miroslawwaldowski/WeatherStation/Weather_Station_Visualisation/Weather_Station_Electronics.png

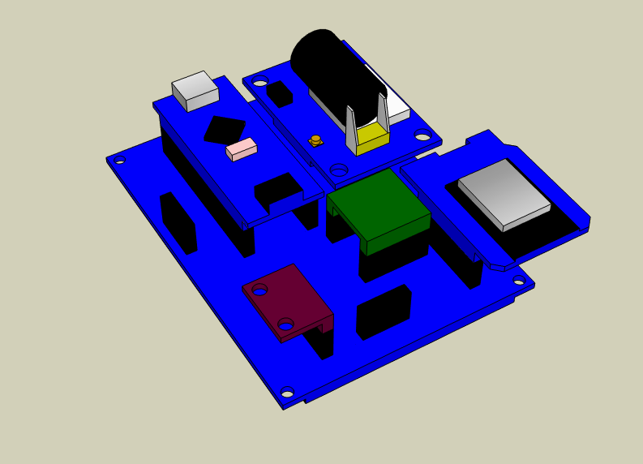
Weather_Station_Visualisation/Weather_Station_Electronics.png
