miroslawwaldowski/WeatherStation/Weather_Station_Visualisation/Weather_Station_Interior.png

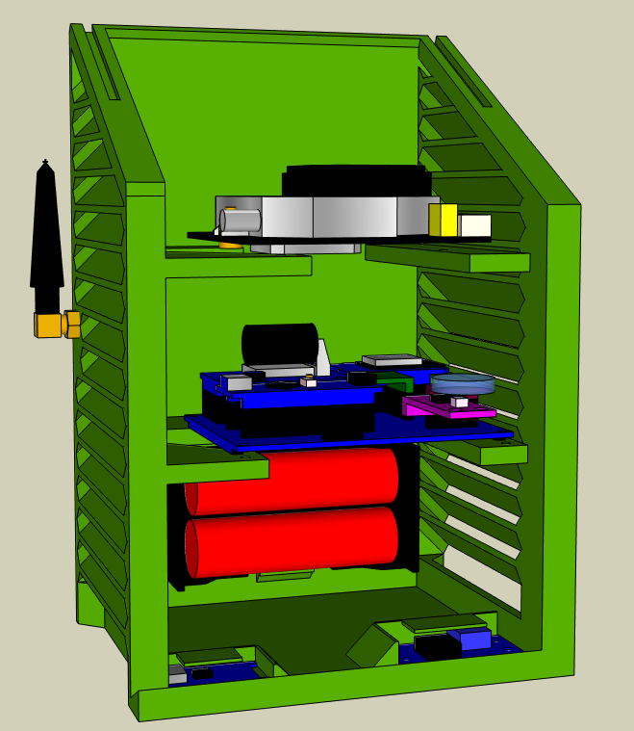
Weather_Station_Visualisation/Weather_Station_Interior.png
