miroslawwaldowski/WeatherStation/Weather_Station_Visualisation/Weather_Station_Whole.png

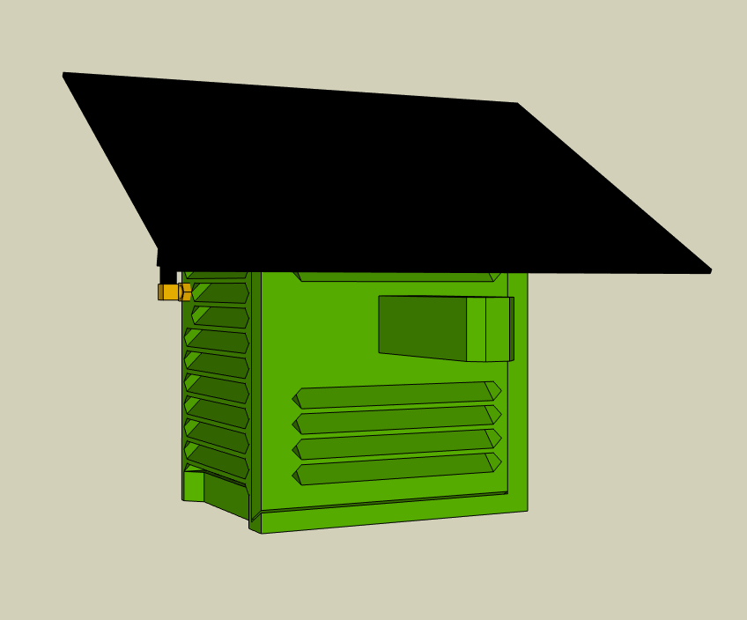
Weather_Station_Visualisation/Weather_Station_Whole.png
