miroslawwaldowski/WeatherStation/Weather_Station_Assembly_Images/08.jpg

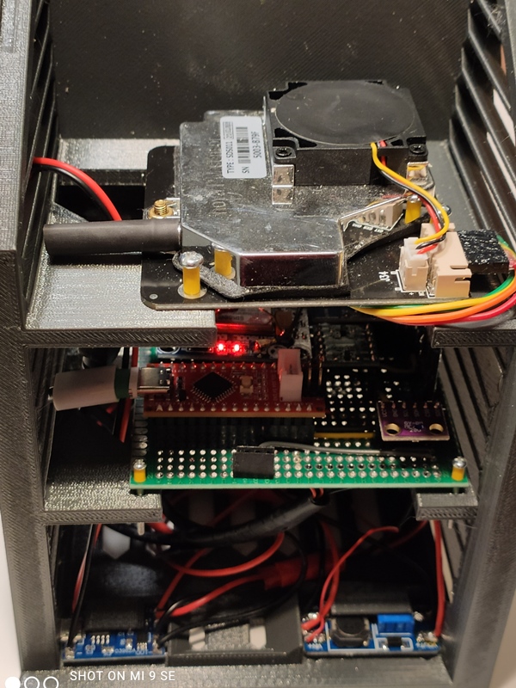
Weather_Station_Assembly_Images/08.jpg
